mrWheel/handheldAerosolSensor/documents/ESP32 DEVKIT V1 (30pins).png

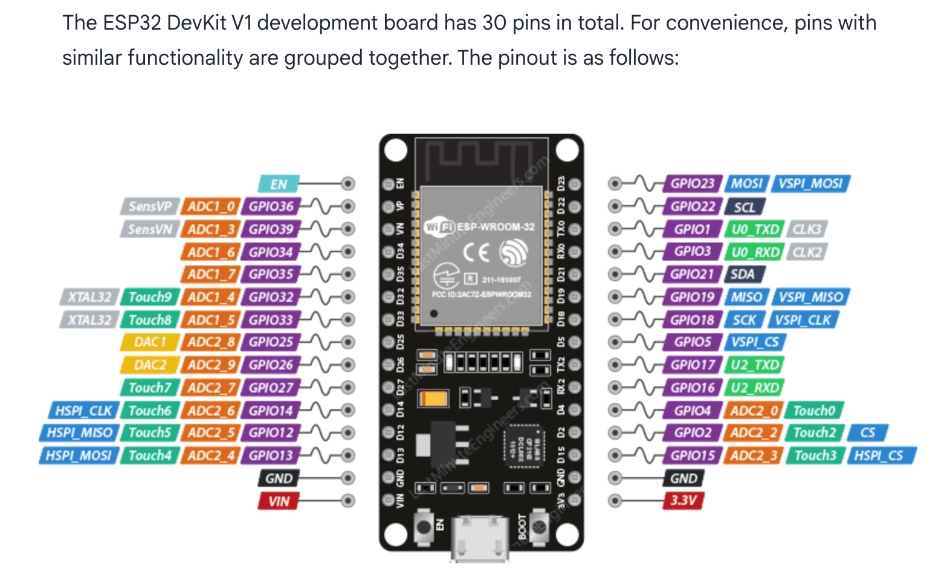
documents/ESP32 DEVKIT V1 (30pins).png
