mrWheel/handheldAerosolSensor/documents/GY-MB-P:E-280.png

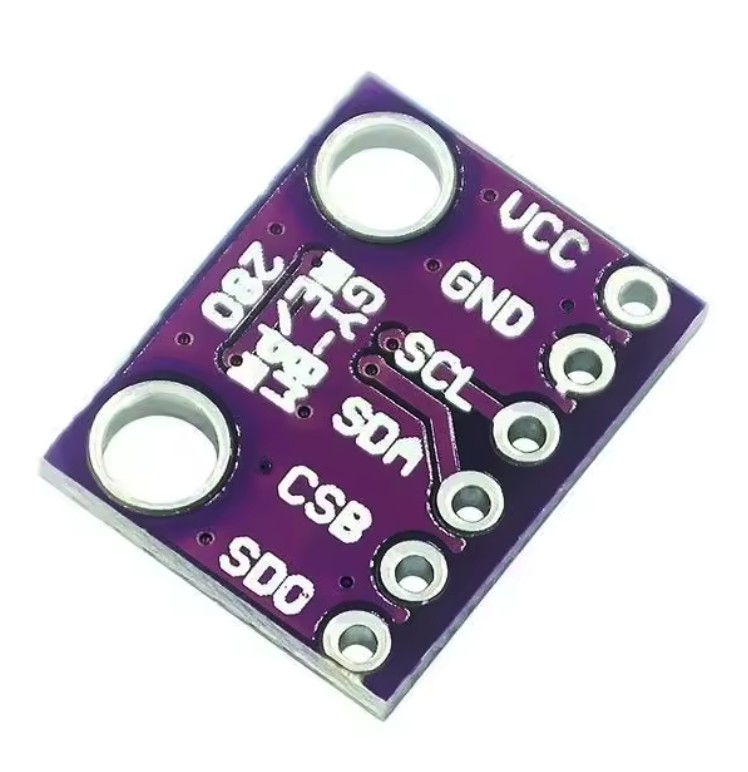
documents/GY-MB-P:E-280.png
