mrWheel/handheldAerosolSensor/documents/hAS_Top3Da.png

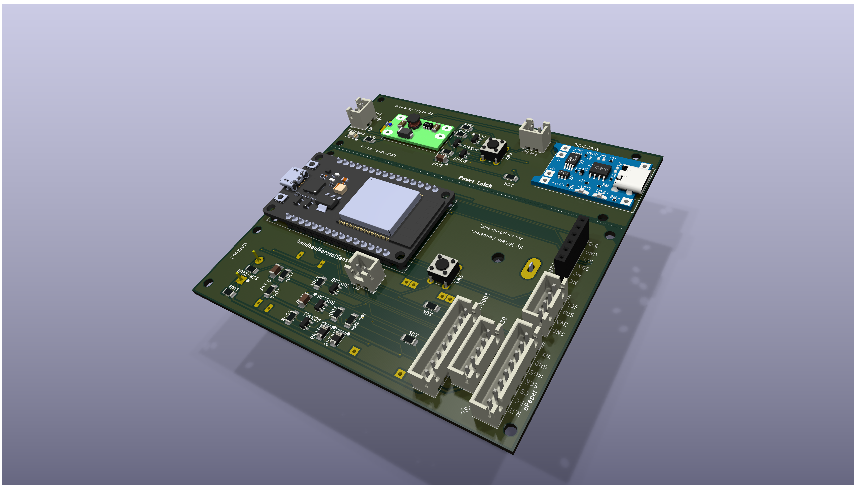
documents/hAS_Top3Da.png
