mrWheel/handheldAerosolSensor/documents/hAS_Top_Dim.png

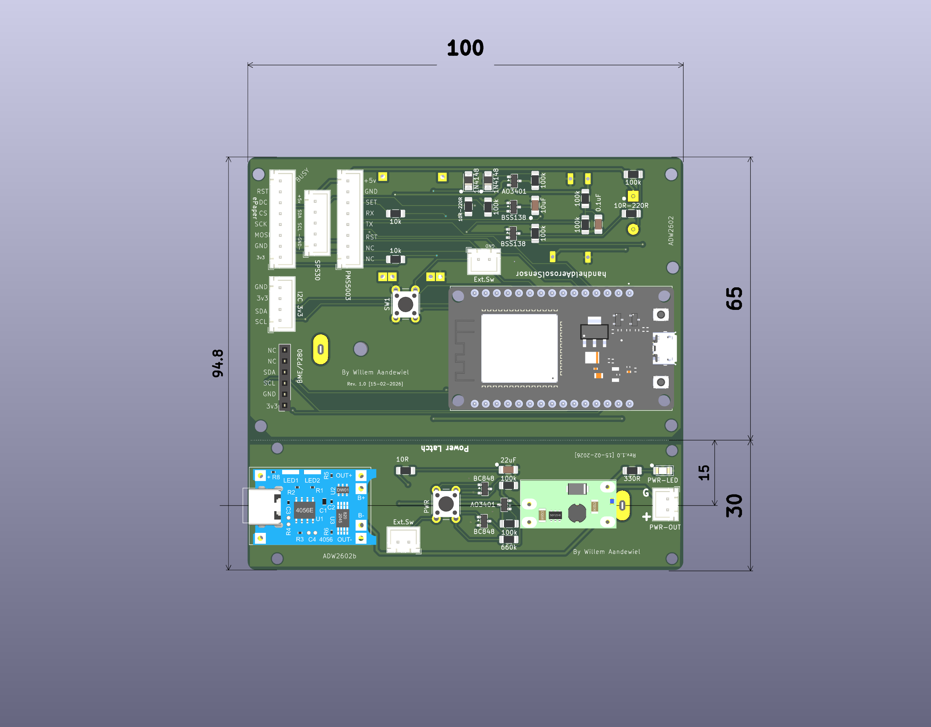
documents/hAS_Top_Dim.png
