mrWheel/handheldAerosolSensor/documents/SPS30.png

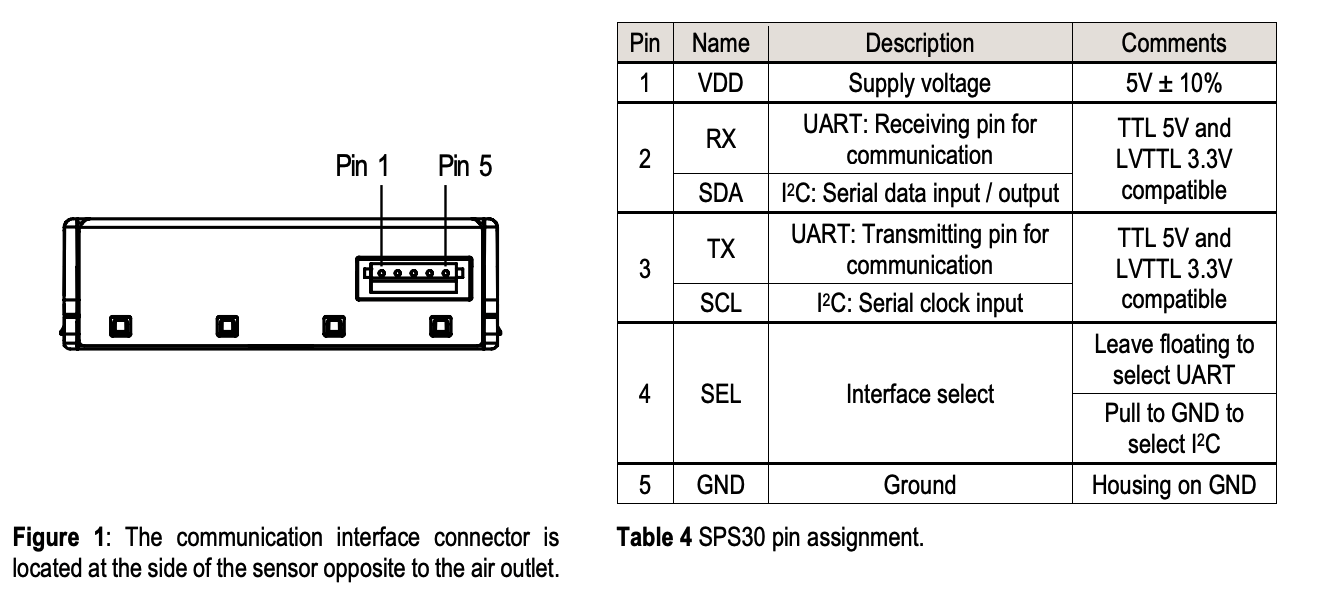
documents/SPS30.png
